LED-BOY/Ledboy-MINI/Game Sources/SpaceInvadersLight_1.4/SpaceInvadersLight_1.4.ino

/* SpaceInvadersLight 1.4 for LEDBOY MINI / ATtiny series 0, 1 and 2.
  Flash CPU Speed 5MHz.
  this code is released under GPL v3, you are free to use and modify.
  released on 2022.

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
    To contact us: ledboy.net
    ledboyconsole@gmail.com
*/
#include "tinyOLED.h"
#include "sprites.h"
#include <avr/interrupt.h>
#include <avr/sleep.h>
#include <avr/eeprom.h>

#if defined(MILLIS_USE_TIMERA0) || defined(MILLIS_USE_TIMERB0)
#error "This sketch does't use TCA0 nor TCB0 to save flash, select Disabled."
#endif

#define SCREEN_ON PORTC.OUT &= ~PIN0_bm;  // P CHANNEL mosfet low to activate
#define SCREEN_OFF PORTC.OUT |= PIN0_bm;  // P CHANNEL mosfet high to deactivate
#define BUTTONLOW !(PORTC.IN & PIN3_bm)   // button press low
#define BUTTONHIGH (PORTC.IN & PIN3_bm)   // button not pressed high
#define MAXVOLTAGE 4100                   // max voltage allowed to the battery
#define MINVOLTAGE 3200                   // min voltage allowed to be operational
#define BATTCHR !(PORTA.IN & PIN4_bm)     // battery charging

#define EEPROM_SOUND 125
#define EEPROM_SCORE 126
#define MAX_LEVEL 20
#define ALL_ENEMIES_DEAD 0x3F

int8_t lives = 2;
uint8_t gameLevel = 1;
uint8_t gameSpeed = 0;  // controls game speed lower number faster game
uint16_t score = 0;
uint16_t timer = 0;
bool showIntro = true;
bool startGame = false;
volatile uint8_t interruptDebounce = 0;
volatile uint16_t interruptTimer = 0;
volatile bool sound = true;

void setup() {
  //_PROTECTED_WRITE(WDT.CTRLA, WDT_PERIOD_4KCLK_gc);// enable watchdog 4 sec. aprox.
  PORTA.DIR = 0b00000000;                   // setup ports in and out //  pin2 (GREEN) on
  PORTB.DIR = 0b00000011;                   // setup ports in and out
  PORTC.DIR = 0b00000011;                   // setup ports in and out
  PORTC.PIN3CTRL = PORT_PULLUPEN_bm;        // button pullup
  PORTC.PIN2CTRL = PORT_PULLUPEN_bm;        // sensor pullup
  PORTA.PIN4CTRL = PORT_ISC_BOTHEDGES_gc | PORT_PULLUPEN_bm;;  //attach interrupt to portA pin 4 keeps pull up enabled, charge pin pullup
 
  TCB0.CCMP = 5000;                  // Set compare value for 1ms (5 MHz clock)
  TCB0.CTRLA = TCB_CLKSEL_CLKDIV1_gc | TCB_ENABLE_bm; // Enable TCB0 with no prescaler
  TCB0.INTCTRL = TCB_CAPT_bm;        // Enable interrupt

  //sei();                                             // enable interrupts
  set_sleep_mode(SLEEP_MODE_PWR_DOWN);               // configure sleep mode
  _PROTECTED_WRITE(WDT.CTRLA, WDT_PERIOD_4KCLK_gc);  // enable watchdog 4 sec. aprox.

  // reset hi score
  while (BUTTONLOW || interruptTimer < 300) {

    if (interruptTimer > 4000) {  // clear HI score
      writeScoreToEEPROM(EEPROM_SCORE, 0);
      while (BUTTONLOW);
      break;  // write only once; repeated EEPROM writes shorten its life
    }
  }
  oled.begin();  // start oled screen
  oled.clearScreen();
  _PROTECTED_WRITE(WDT.CTRLA, 0);  // disable watchdog

  // Sound preference is stored as 0 or 1. Erased EEPROM defaults to sound on.
  uint8_t savedSound = eeprom_read_byte((uint8_t *)EEPROM_SOUND);
  sound = (savedSound > 1) ? true : savedSound;

  if (BATTCHR) {
    drawSprite(4, 0, battIcon);
    goToSleep();
  }
}

void loop() {
  // Display the intro screen if the `showIntro` flag is set
  if (showIntro) {
    introScreen();
  }

  // Check for button press to start the game
  if (buttonDebounce(200)) {
    game();
  }

  // Handle sleep timer feedback
  if ((interruptTimer - timer) > 1000) {
    uint8_t arrowPos = 42;  // Initial position for the first arrow

    // Draw arrows to indicate the elapsed time towards sleep mode
    for (uint8_t x = 0; x < (interruptTimer - timer) / 1000; x++) {
      drawSprite(arrowPos, 3, arrowRight);  // Draw an arrow
      arrowPos += 15;  // Move the position for the next arrow
    }
  }

  // Enter sleep mode after 6 seconds of inactivity
  if ((interruptTimer - timer) > 6000) {
    goToSleep();
  }
}

void introScreen(void) {
  // Clear the screen
  oled.clearScreen();

  // Draw level indicator
  drawSprite(40, 1, letterL);  // Letter 'L'
  drawSprite(48, 1, letterE);  // Letter 'E'
  drawSprite(56, 1, letterV);  // Letter 'V'
  drawSprite(64, 1, letterE);  // Letter 'E'
  drawSprite(72, 1, letterL);  // Letter 'L'
  drawDecimal(52, 2, gameLevel);  // Display current game level

  // Draw sleep timer label
  drawSprite(0, 3, letterS);   // Letter 'S'
  drawSprite(8, 3, letterL);   // Letter 'L'
  drawSprite(16, 3, letterE);  // Letter 'E'
  drawSprite(24, 3, letterE);  // Letter 'E'
  drawSprite(32, 3, letterP);  // Letter 'P'

  // Display high score and battery status if the game hasn't started yet
  if (!startGame) {
    // Draw high score label
    drawSprite(92, 0, letterH);   // Letter 'H'
    drawSprite(100, 0, letterI);  // Letter 'I'
    showScore(readScoreFromEEPROM(EEPROM_SCORE));  // Display high score from EEPROM

    // Draw battery icon and percentage
    drawSprite(4, 0, battIcon);  // Battery icon
    drawDecimal(0, 1, voltageReading());  // Display battery percentage

    // Reset game state
    startGame = true;
    score = 0;
  }

  // Reset intro screen flag and update timer
  showIntro = false;
  timer = interruptTimer;
}

// Main game function
void game() {
  int8_t enemiesPosX = 0;
  int8_t lastEnemiesPosX = 0;
  uint8_t mothershipPosX = 102;
  //uint8_t lastMothershipPosX = 0;
  uint8_t playerPos = 20;
  uint8_t enemiesPosY = 0;
  uint8_t enemiesSpeed = (180 - gameSpeed);
  uint8_t newEnemiesYPos = 0;
  uint8_t lastPlayerPos = 20;
  uint8_t playerShotState = 0;
  uint8_t enemiesShotState = 0;
  uint8_t playerFirePosX = 0;
  int8_t enemiesFirePosX = 0;
  int8_t playerFirePosY = 3;
  int8_t enemiesFirePosY = 0;
  uint8_t enemiesKilled = 0;  // one bit per invader; faster and smaller than an array
  uint8_t enemiesKilledCounter = 0;
  uint16_t enemiesFireTimer = 0;
  uint16_t playerFireTimer = 0;
  uint16_t enemiesTimer = 0;
  uint16_t playerTimer = 0;
  uint16_t mothershipTimer = 0;
  uint16_t mothershipSpawnTimer = interruptTimer;
  bool enemiesMoveRight = true;
  // bool enemiesPosXEven = true;
  bool playerFireAgain = true;
  bool enemiesFireAgain = true;
  bool mothershipIsDead = true;
  bool soundStatus = !sound;

  // Draw initial screen elements
  oled.clearScreen();
  drawSprite(4, 0, battIcon);
  drawDecimal(0, 1, voltageReading());  // Display battery percentage
  showScore(0);

  // Draw screen bars
  for (uint8_t x = 0; x < 4; x++) {
    oled.drawLine(18, x, 1, 0b11111111);
    oled.drawLine(110, x, 1, 0b11111111);
  }

  // Draw player lives on screen
  for (uint8_t x = 0; x < lives; x++) {
    drawSprite(116, x + 2, ship);
  }

  // Main game loop
  while (true) {
    // Handle sound status
    if (soundStatus != sound) {
      soundStatus = sound;
      eeprom_update_byte((uint8_t *)(uintptr_t)EEPROM_SOUND, sound);
      if (sound) {
        drawSprite(2, 3, letterS);  // Show 'S' for sound on
      } else {
        drawSprite(2, 3, letterM);  // Show 'M' for mute
      }
      delay(800);
      PORTA.DIR = 0b00000000;
      PORTC.PIN2CTRL |= PORT_ISC_RISING_gc;  // Attach interrupt to portC pin 2
    }

    // Handle battery display update
    if ((interruptTimer - timer) > 16000) {
      timer = interruptTimer;
      for (uint8_t x = 0; x < 2; x++) {
        oled.drawLine(20, (newEnemiesYPos + x), 90, 0x00);  // Clear enemy position
      }
      newEnemiesYPos++;
      drawDecimal(0, 1, voltageReading());  // Update battery percentage
    }

    // Spawn mothership
    if ((uint16_t)(interruptTimer - mothershipSpawnTimer) > 6000 && mothershipIsDead && newEnemiesYPos > 0) {
      mothershipIsDead = false;
      mothershipSpawnTimer = interruptTimer;
    }

    // Mothership movement logic
    if ((interruptTimer - mothershipTimer) > 35 && !mothershipIsDead) {
      mothershipTimer = interruptTimer;
      oled.drawLine(mothershipPosX, 0, 8, 0x00);  // Clear mothership position

      if (mothershipPosX--, mothershipPosX < 20) {
        mothershipIsDead = true;  // Mothership reaches end of screen
        mothershipPosX = 102;
      } else {
        drawSprite(mothershipPosX, 0, mothership);
      }
    }

    // Check if player hits mothership
    if (playerFirePosX >= mothershipPosX && playerFirePosX < (mothershipPosX + 8) && playerFirePosY == 0 && !mothershipIsDead) {
      drawSprite(mothershipPosX, 0, explosion);  // Draw explosion sprite
      beep(250, 100);
      oled.drawLine(mothershipPosX, 0, 8, 0x00);  // Clear mothership position
      mothershipIsDead = true;
      playerFireAgain = true;
      mothershipPosX = 102;
      showScore(10);

      // Grant extra life if applicable
      if (lives < 2) {
        lives++;
        for (uint8_t x = 0; x < lives; x++) {
          drawSprite(116, x + 2, ship);
        }
      }
    }

    // Enemies movement and kill logic
    if ((interruptTimer - enemiesTimer) > enemiesSpeed) {
      enemiesTimer = interruptTimer;
      enemiesPosX += enemiesMoveRight ? 1 : -1;
      beep(250, 4);

      for (uint8_t x = 0; x < sizeof(enemiesPattern) / sizeof(uint8_t); x++) {
        if (!(enemiesKilled & _BV(x))) {
          if ((enemiesPattern[x] + enemiesPosX) > 102 && enemiesMoveRight) {
            enemiesMoveRight = false;
          }

          if ((enemiesPattern[x] + enemiesPosX) < 26 && !enemiesMoveRight) {
            enemiesMoveRight = true;
          }

          if (enemiesFireAgain && ((interruptTimer + x) & 0x07) == 0) {
            enemiesFirePosX = (enemiesPattern[x] + enemiesPosX);
            enemiesFireAgain = false;
          }

          enemiesPosY = (x % 2) + newEnemiesYPos;

          if (playerFirePosX >= (enemiesPattern[x] + enemiesPosX) && playerFirePosX < (enemiesPattern[x] + enemiesPosX) + 8 && playerFirePosY == enemiesPosY) {
            enemiesKilled |= _BV(x);
            enemiesKilledCounter++;
            playerFireAgain = true;
            drawSprite((enemiesPattern[x] + lastEnemiesPosX), enemiesPosY, explosion);
            beep(250, 100);
            oled.drawLine((enemiesPattern[x] + lastEnemiesPosX), enemiesPosY, 8, 0x00);
            showScore(2);

            if (enemiesKilledCounter > 3) {
              enemiesSpeed = (40 - gameLevel);
            }
          } else {
            oled.drawLine((enemiesPattern[x] + lastEnemiesPosX), enemiesPosY, 8, 0x00);

            if (enemiesPosX % 2 == 0) {
              drawSprite(enemiesPattern[x] + enemiesPosX, enemiesPosY, enemy1A);
            } else {
              drawSprite(enemiesPattern[x] + enemiesPosX, enemiesPosY, enemy1B);
            }
          }
        }
      }
      lastEnemiesPosX = enemiesPosX;

      if (enemiesKilled == ALL_ENEMIES_DEAD) {
        showScore(gameLevel);  // wave-clear bonus
        if (gameLevel < MAX_LEVEL) {
          gameLevel++;
          gameSpeed += 5;
        } else {
          // Completing the final wave starts a harder new run instead of
          // leaving the game stuck forever with no enemies.
          gameLevel = 1;
          gameSpeed = 0;
        }
        break;
      }
    }

    // Player fire logic
    if ((interruptTimer - playerFireTimer) > 120) {
      playerFireTimer = interruptTimer;
      oled.drawLine(playerFirePosX, playerFirePosY, 1, 0b00000000);

      if (playerFireAgain) {
        playerFirePosX = (playerPos + 4);
        playerFirePosY = 2;
        playerShotState = 0;
        playerFireAgain = false;
      }

      if (playerShotState > 6) {
        playerShotState = 0;
        playerFirePosY--;

        if (playerFirePosY < 0) {
          playerFireAgain = true;
        }
      }

      if (!playerFireAgain) {
        oled.drawLine(playerFirePosX, playerFirePosY, 1, (0b11000000 >> playerShotState));
        playerShotState++;
      }
    }

    // Enemies fire logic
    if ((interruptTimer - enemiesFireTimer) > 120 && !enemiesFireAgain) {
      enemiesFireTimer = interruptTimer;
      oled.drawLine(enemiesFirePosX, enemiesFirePosY, 1, 0b00000000);

      if (enemiesShotState > 6) {
        enemiesShotState = 0;
        enemiesFirePosY++;

        if (enemiesFirePosY > 3) {
          enemiesFirePosY = enemiesPosY;
          enemiesShotState = 6;
          enemiesFireAgain = true;
        }
      }

      if (!enemiesFireAgain) {
        oled.drawLine(enemiesFirePosX, enemiesFirePosY, 1, (0b00000011 << enemiesShotState));
        enemiesShotState++;
      }
    }

    // Player movement logic
    if ((interruptTimer - playerTimer) > 50) {
      playerTimer = interruptTimer;

      if (lastPlayerPos != playerPos) {
        lastPlayerPos = playerPos;
        oled.drawLine(20, 3, 90, 0x00);
      }

      if (BUTTONLOW && playerPos < 103) {
        playerPos++;
      } else if (playerPos > 20) {
        playerPos--;
      }
      drawSprite(playerPos, 3, ship);
    }

    // Check if player is hit
    if ((enemiesFirePosX >= playerPos && enemiesFirePosX < (playerPos + 8) && enemiesFirePosY == 3) || enemiesPosY > 2) {
      for (uint8_t x = 0; x < 10; x++) {
        drawSprite(playerPos, 3, explosion);
        beep(250, 60);
        oled.drawLine(playerPos, 3, 8, 0x00);
        beep(250, 60);
      }

      if (lives--, lives < 0) {
        if (score > readScoreFromEEPROM(EEPROM_SCORE)) {
          writeScoreToEEPROM(EEPROM_SCORE, score);
        }
        gameLevel = 1;
        score = 0;
        gameSpeed = 0;
        lives = 2;
      }
      break;  // End game loop
    }
  }

  PORTC.PIN2CTRL &= ~PORT_ISC_gm;
  showIntro = true;
  timer = interruptTimer;
}

void showScore(uint16_t addScore) {  // draws all ledInvadersScore using showTime function

  if (score += addScore, score > 9999) score = 9999;
  uint16_t valueDecimals = score;

  if (score < 100) {  // functions to draw units in digit 3, decimals in digit 2 and hundredths in digit 1
    drawDecimal(112, 0, 0);
    drawDecimal(112, 1, score);
  } else {
    drawDecimal(112, 0, (score / 100));
    drawDecimal(112, 1, (valueDecimals - ((score / 100) * 100)));
  }
}

void writeScoreToEEPROM(uint8_t address, uint16_t number) {    // ledInvadersScore is an uint16_t so needs to be stored in 2 eeprom slots of 8bits
  eeprom_update_byte((uint8_t *)(uintptr_t)address, number >> 8);
  eeprom_update_byte((uint8_t *)(uintptr_t)(address + 1), number);
}

uint16_t readScoreFromEEPROM(uint8_t address) {  // reads and reconstruct the number
  byte byte1 = eeprom_read_byte((uint8_t *)(uintptr_t)address);
  byte byte2 = eeprom_read_byte((uint8_t *)(uintptr_t)(address + 1));

  uint16_t value = ((uint16_t)byte1 << 8) | byte2;
  return value > 9999 ? 0 : value;  // erased/corrupt EEPROM must not become 65535
}

bool buttonDebounce(uint16_t debounceDelay) {

  if (BUTTONHIGH) return false;
  timer = interruptTimer;

  while ((interruptTimer - timer) < debounceDelay || BUTTONLOW);
  return true;
}

void drawSprite(uint8_t column, uint8_t page, const uint8_t* sprite) {
  oled.setCursor(column, page);  // position cursor column - page
  oled.ssd1306_send_data_start();

  for (uint8_t x = 0; x < 8; x++) {
    oled.ssd1306_send_data_byte(sprite[x]);
  }
  oled.ssd1306_send_data_stop();
}

void drawDecimal(uint8_t firstPixel, uint8_t page, uint8_t value) {
  // Always draw 2 digits
  uint8_t tensDigit = value / 10;  // Extract the tens digit
  uint8_t unitsDigit = value % 10; // Extract the units digit

  // Draw the tens digit (or 0 if value is less than 10)
  drawSprite(firstPixel, page, numbers[tensDigit]);

  // Draw the units digit
  drawSprite(firstPixel + 8, page, numbers[unitsDigit]);
}

void beep(uint8_t freq, uint16_t delayTime) {  // sound function

  if (sound) analogWrite(PIN_PC1, freq);
  delay(delayTime);
  turnOffPWM(PIN_PC1);
}

void goToSleep(void) {

  if (!BATTCHR) {
    //oled.clearScreen();
    SCREEN_OFF;
  }
  PORTC.PIN3CTRL |= PORT_ISC_BOTHEDGES_gc;  //attach interrupt to portC pin 3 keeps pull up enabled
  //PORTC.PIN2CTRL &= ~PORT_ISC_gm; // disable sensor interrupt
  //_PROTECTED_WRITE(WDT.CTRLA, 0);
  //TCA0.SPLIT.CTRLA = 0; //disable TCA0 and set divider to 1
  //TCA0.SPLIT.CTRLESET = TCA_SPLIT_CMD_RESET_gc | 0x03; //set CMD to RESET to do a hard reset of TCA0.
  TCB0.INTCTRL &= ~TCB_CAPT_bm; // Disable the capture interrupt
  TCB0.INTFLAGS = TCB_CAPT_bm;  // Clear the interrupt flag
  sleep_enable();
  sleep_cpu();  // go to sleep
}

// Read Supply Voltage (in millivolts)
uint16_t readSupplyVoltage() {
  ADC0.CTRLA = ADC_ENABLE_bm; // Enable ADC
  analogReference(VDD); // Set reference voltage to VDD
  VREF.CTRLA = VREF_ADC0REFSEL_1V5_gc; // Set internal reference to 1.5V

  // Take two readings to ensure accuracy (first reading may be invalid)
  uint32_t reading = analogRead(ADC_INTREF);
  reading = analogRead(ADC_INTREF);

  // Convert ADC reading to millivolts
  uint32_t intermediate = 1023UL * 1500; // 1023 * 1.5V reference
  reading = intermediate / reading; // Calculate voltage in mV
  return reading;
}

uint8_t voltageReading(void) {
  uint16_t millivolts = readSupplyVoltage();
  uint8_t percent;
  if (millivolts <= MINVOLTAGE) percent = 1;
  else if (millivolts >= MAXVOLTAGE) percent = 99;
  else percent = (millivolts - MINVOLTAGE) / 9;

  if (percent < 5) goToSleep();  // prevent complete battery discharge
  return percent;
}

ISR(TCB0_INT_vect) {
  /* The interrupt flag has to be cleared manually */
  TCB0_INTFLAGS = 1;  // clear flag
  interruptTimer++;
  if (interruptTimer % 100 == 0) interruptDebounce = 0;
  // wdt_reset(); // reset watchdog
}

ISR(PORTA_PORT_vect) {
  _PROTECTED_WRITE(RSTCTRL.SWRR, 1);
}

ISR(PORTC_PORT_vect) {  // turn sound off or on by shaking the device

  if (PORTC.INTFLAGS & PIN3_bm) {
    _PROTECTED_WRITE(RSTCTRL.SWRR, 1);
  }

  if (PORTC.INTFLAGS & PIN2_bm) {
    VPORTC.INTFLAGS = (1 << 2);

    if (interruptDebounce++, interruptDebounce > 4) {  // interrupt debounce
      PORTC.PIN2CTRL &= ~PORT_ISC_gm;
      PORTA.DIR = (1 << 6);
      interruptDebounce = 0;
      sound = !sound;
    }
  }
}
