LED-BOY/Ledboy-MINI/App Sources/ledboy_MINI_watch_3.1/digits.h

/*
    This file is part of Game&Light Timer

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
    To contact us: ledboy.net
    ledboyconsole@gmail.com
*/
//  numbers
const uint8_t numbers[10][28] = {

  // 0
  {
    0xfc, 0xff, 0x07, 0x07, 0x07, 0x07, 0x07,
    0x07, 0x07, 0x07, 0x07, 0x07, 0xff, 0xfc,
    0x3f, 0xff, 0xe0, 0xe0, 0xe0, 0xe0, 0xe0,
    0xe0, 0xe0, 0xe0, 0xe0, 0xe0, 0xff, 0x3f
  },

  // 1
  {
    0x00, 0x00, 0x00, 0x00, 0x00, 0x00, 0x00,
    0x00, 0x00, 0x00, 0x00, 0x00, 0x00, 0x00,
    0x20, 0xe0, 0xe0, 0xe0, 0xe0, 0xe0, 0xe0,
    0xe0, 0xe0, 0xe0, 0xe0, 0xe0, 0xe0, 0x20
  },

  // 2
  {
    0xfc, 0xff, 0x07, 0x07, 0x07, 0x07, 0xff,
    0x00, 0x00, 0x00, 0x00, 0x00, 0xff, 0xfc,
    0x3f, 0xff, 0x00, 0x00, 0x00, 0x00, 0x3f,
    0xf0, 0xe0, 0xe0, 0xe0, 0xe0, 0xff, 0x3f
  },

  // 3
  {
    0xfc, 0xff, 0x00, 0x00, 0x00, 0x00, 0xc0,
    0x00, 0x00, 0x00, 0x00, 0x00, 0xff, 0xfc,
    0x3f, 0xff, 0xe0, 0xe0, 0xe0, 0xe0, 0xff,
    0xf0, 0xe0, 0xe0, 0xe0, 0xe0, 0xff, 0x3f
  },

  // 4
  {
    0x00, 0x00, 0x00, 0x00, 0x00, 0x00, 0xfc,
    0x0f, 0x07, 0x07, 0x07, 0x07, 0x07, 0x04,
    0x20, 0xe0, 0xe0, 0xe0, 0xe0, 0xe0, 0xff,
    0xf0, 0xe0, 0xe0, 0xe0, 0xe0, 0xe0, 0x20
  },

  // 5
  {
    0xfc, 0xff, 0x00, 0x00, 0x00, 0x00, 0x00,
    0xff, 0x07, 0x07, 0x07, 0x07, 0xff, 0xfc,
    0x3f, 0xff, 0xe0, 0xe0, 0xe0, 0xe0, 0xf0,
    0x3f, 0x00, 0x00, 0x00, 0x00, 0xff, 0x3f
  },

  // 6
  {
    0xfc, 0x0f, 0x07, 0x07, 0x07, 0x07, 0xff,
    0x0f, 0x07, 0x07, 0x07, 0x07, 0x07, 0x01,
    0x3f, 0xf0, 0xe0, 0xe0, 0xe0, 0xe0, 0xff,
    0x00, 0x00, 0x00, 0x00, 0x00, 0x00, 0x00
  },

  // 7
  {
    0x00, 0x00, 0x00, 0x00, 0x00, 0x00, 0x00,
    0x00, 0x00, 0x00, 0x00, 0x00, 0xfc, 0xff,
    0x20, 0xe0, 0xe0, 0xe0, 0xe0, 0xe0, 0xe0,
    0xe0, 0xe0, 0xe0, 0xe0, 0xe0, 0xff, 0x3f
  },

  // 8
  {
    0xfc, 0xff, 0x07, 0x07, 0x07, 0x07, 0xff,
    0x0f, 0x07, 0x07, 0x07, 0x07, 0xff, 0xfc,
    0x3f, 0xff, 0xe0, 0xe0, 0xe0, 0xe0, 0xff,
    0xf0, 0xe0, 0xe0, 0xe0, 0xe0, 0xff, 0x3f
  },

  // 9
  {
    0x00, 0x00, 0x00, 0x00, 0x00, 0x00, 0xfc,
    0x0f, 0x07, 0x07, 0x07, 0x07, 0xff, 0xfc,
    0x20, 0xe0, 0xe0, 0xe0, 0xe0, 0xe0, 0xff,
    0xf0, 0xe0, 0xe0, 0xe0, 0xe0, 0xff, 0x3f
  }
};
